AEFeinstein/PixelShirtV2/Firmware/PixelShirtV2/PixelShirtV2.h

/*
 * PixelShirtV2.h
 *
 *  Created on: Dec 24, 2015
 *      Author: adam
 */

#ifndef PIXELSHIRTV2_H_
#define PIXELSHIRTV2_H_

#ifndef ARDUINO
void setup(void);
void loop(void);
#endif

void switchGame(void);

#endif /* PIXELSHIRTV2_H_ */
