AEFeinstein/PixelShirtV2/Firmware/PixelShirtV2/ScoreDisplay.h

/*
 * ScoreDisplay.h
 *
 *  Created on: Dec 24, 2015
 *      Author: adam
 */

#ifndef SCOREDISPLAY_H_
#define SCOREDISPLAY_H_

void DisplayScore(uint16_t score, uint32_t rgb);
void DrawNumber(uint8_t number, uint8_t offsetX, uint8_t offsetY, uint32_t rgb);

#endif /* SCOREDISPLAY_H_ */
